Kingyumu/baobao/src/state.rs

//! 应用状态机 — 传感器读数、页面、闹钟、气压趋势等业务逻辑。
//!
//! 与 UI（display/render）和网络（network）解耦：主循环读硬件后更新 [`SystemState`]，
//! 渲染层只读 state，不直接访问 I2C/WiFi。
//!
//! ## Rust 要点
//! - `enum`：用类型表达有限状态（页面、气压趋势），比魔法字符串安全
//! - `impl Enum { fn next(self) -> Self }`：`self` 按值传递，状态转换返回新枚举
//! - 环形缓冲区：`(idx + 1) % N` 实现固定长度历史，无 Vec 分配
//! - `Option<(u8,u8)>`：记录「某天是否已响铃」，避免同一天重复触发

use crate::config;
use crate::sensors::DateTime;

/// 根据最近 10 次气压采样比较前/后半段均值。
#[derive(Debug, Clone, Copy, PartialEq)]
pub enum PressureTrend {
    Rising,
    Stable,
    Falling,
}

/// 触摸屏短按在本地页与对方城市页之间切换。
#[derive(Debug, Clone, Copy, PartialEq)]
pub enum DisplayPage {
    Local,
    Partner,
}

impl DisplayPage {
    pub fn next(self) -> Self {
        match self {
            Self::Local => Self::Partner,
            Self::Partner => Self::Local,
        }
    }

    pub fn label(self) -> &'static str {
        match self {
            Self::Local => "本地",
            Self::Partner => "对方",
        }
    }
}

/// 从中国天气网 HTTP 接口解析出的室外数据。
#[derive(Debug, Clone)]
pub struct NetworkWeather {
    pub temp: f32,
    pub humidity: f32,
    pub text: heapless::String<32>,
    pub weather_code: heapless::String<8>,
}

/// 全局运行时状态（单线程主循环独占 `&mut`，无需 Arc/Mutex）。
pub struct SystemState {
    pub temperature: f32,
    pub humidity: f32,
    pub pressure: f32,
    pressure_history: [f32; 10],
    pressure_idx: usize,
    pub pressure_filled: bool,
    pub pressure_trend: PressureTrend,
    pub current_time: Option<DateTime>,
    pub weather_code: heapless::String<8>,
    pub wifi_connected: bool,
    pub network_weather: Option<NetworkWeather>,
    pub partner_weather: Option<NetworkWeather>,
    pub together_days: u32,
    pub animation_counter: u32,
    pub special_event: Option<&'static str>,
    special_event_handled: Option<(u8, u8)>, // (month, day) 已处理标记
    pub last_weather_update: u64,
    pub last_ntp_sync: u64,
    pub display_page: DisplayPage,
    temp_chart: [f32; config::TEMP_CHART_LEN],
    chart_idx: usize,
    chart_filled: bool,
    pub chart_tick: u32,
    last_chart_sample: u64,
    pub weather_alert_active: bool,
    weather_alert_until: u64,
    last_weather_alert: u64,
    last_hourly_chime: Option<(u8, u8, u8)>,
    alarm_handled: Option<(u8, u8)>,
}

impl SystemState {
    pub fn new() -> Self {
        let mut wc = heapless::String::new();
        wc.push_str("d01").unwrap();
        Self {
            temperature: 0.0,
            humidity: 0.0,
            pressure: 1013.0,
            pressure_history: [1013.0; 10],
            pressure_idx: 0,
            pressure_filled: false,
            pressure_trend: PressureTrend::Stable,
            current_time: None,
            weather_code: wc,
            wifi_connected: false,
            network_weather: None,
            partner_weather: None,
            together_days: 1,
            animation_counter: 0,
            special_event: None,
            special_event_handled: None,
            last_weather_update: 0,
            last_ntp_sync: 0,
            display_page: DisplayPage::Local,
            temp_chart: [20.0; config::TEMP_CHART_LEN],
            chart_idx: 0,
            chart_filled: false,
            chart_tick: 0,
            last_chart_sample: 0,
            weather_alert_active: false,
            weather_alert_until: 0,
            last_weather_alert: 0,
            last_hourly_chime: None,
            alarm_handled: None,
        }
    }

    /// 写入新气压并更新趋势（需凑满 10 点后才计算）。
    pub fn update_pressure(&mut self, p: f32) {
        self.pressure = p;
        self.pressure_history[self.pressure_idx] = p;
        self.pressure_idx = (self.pressure_idx + 1) % 10;
        if self.pressure_idx == 0 {
            self.pressure_filled = true;
        }
        if !self.pressure_filled {
            return;
        }
        // 前 5 点 vs 后 5 点均值差
        let (old, new) = self.pressure_history[..10].iter().enumerate().fold(
            (0.0f32, 0.0f32),
            |(o, n), (i, &v)| {
                if i < 5 {
                    (o + v, n)
                } else {
                    (o, n + v)
                }
            },
        );
        let diff = new / 5.0 - old / 5.0;
        self.pressure_trend = if diff > 0.5 {
            PressureTrend::Rising
        } else if diff < -0.5 {
            PressureTrend::Falling
        } else {
            PressureTrend::Stable
        };
    }

    pub fn trend_text(&self) -> &'static str {
        match self.pressure_trend {
            PressureTrend::Rising => "↑ 转晴",
            PressureTrend::Stable => "→ 平稳",
            PressureTrend::Falling => "↓ 转阴",
        }
    }

    pub fn update_time(&mut self, t: DateTime) {
        let today = (t.month, t.day);
        if self.special_event_handled.map(|d| d != today).unwrap_or(false) {
            self.special_event_handled = None;
        }
        self.check_special(&t);
        self.together_days = compute_together_days(&t);
        self.current_time = Some(t);
    }

    fn check_special(&mut self, t: &DateTime) {
        if t.month == config::BIRTHDAY_MONTH && t.day == config::BIRTHDAY_DAY {
            self.special_event = Some("生日快乐！");
            return;
        }
        for &(m, d, msg) in config::ANNIVERSARIES {
            if t.month == m && t.day == d {
                self.special_event = Some(msg);
                return;
            }
        }
        self.special_event = None;
    }

    pub fn should_handle_special_event(&self) -> bool {
        let Some(ev) = self.special_event else {
            return false;
        };
        let Some(t) = self.current_time else {
            return false;
        };
        let today = (t.month, t.day);
        self.special_event_handled != Some(today) && !ev.is_empty()
    }

    pub fn mark_special_event_handled(&mut self) {
        if let Some(t) = self.current_time {
            self.special_event_handled = Some((t.month, t.day));
        }
    }

    /// 主界面图标：气压趋势可覆盖网络天气码。
    pub fn display_code(&self) -> &str {
        match self.pressure_trend {
            PressureTrend::Falling if self.pressure < 1000.0 => "trend_rain",
            PressureTrend::Rising if self.pressure > 1013.0 => "trend_sun",
            _ => self.weather_code.as_str(),
        }
    }

    pub fn set_weather_code(&mut self, code: &str) {
        self.weather_code.clear();
        let _ = self.weather_code.push_str(code);
    }

    pub fn next_page(&mut self) {
        self.display_page = self.display_page.next();
    }

    /// 每分钟采样一次室温，写入环形缓冲（供本地页折线图）。
    pub fn sample_temp_chart(&mut self, now: u64) {
        if now.saturating_sub(self.last_chart_sample) < config::TEMP_CHART_INTERVAL {
            return;
        }
        self.last_chart_sample = now;
        self.temp_chart[self.chart_idx] = self.temperature;
        self.chart_idx = (self.chart_idx + 1) % config::TEMP_CHART_LEN;
        if self.chart_idx == 0 {
            self.chart_filled = true;
        }
        self.chart_tick = self.chart_tick.wrapping_add(1);
    }

    pub fn temp_chart_count(&self) -> usize {
        if self.chart_filled {
            config::TEMP_CHART_LEN
        } else {
            self.chart_idx
        }
    }

    pub fn temp_chart_value(&self, i: usize) -> f32 {
        let n = self.temp_chart_count();
        if n == 0 {
            return self.temperature;
        }
        let start = if self.chart_filled {
            self.chart_idx
        } else {
            0
        };
        self.temp_chart[(start + i) % config::TEMP_CHART_LEN]
    }

    /// 气压骤降且绝对值偏低时触发变天预警（带冷却时间）。
    pub fn check_weather_alert(&mut self, now: u64) -> bool {
        if self.weather_alert_active {
            return false;
        }
        if now.saturating_sub(self.last_weather_alert) < config::WEATHER_ALERT_COOLDOWN {
            return false;
        }
        if !self.pressure_filled || self.pressure_trend != PressureTrend::Falling {
            return false;
        }
        if self.pressure >= 1005.0 {
            return false;
        }
        self.last_weather_alert = now;
        true
    }

    pub fn activate_weather_alert(&mut self, now: u64) {
        self.weather_alert_active = true;
        self.weather_alert_until = now + config::WEATHER_ALERT_DURATION;
    }

    pub fn tick_weather_alert(&mut self, now: u64) {
        if self.weather_alert_active && now >= self.weather_alert_until {
            self.weather_alert_active = false;
        }
    }

    pub fn weather_alert_showing(&self) -> bool {
        self.weather_alert_active
    }

    /// 整点报时：仅在 `:00` 的前 2 秒内触发一次。
    pub fn check_hourly_chime(&mut self, t: &DateTime) -> bool {
        if !config::HOURLY_CHIME_ENABLED {
            return false;
        }
        if t.minute != 0 || t.second >= 2 {
            return false;
        }
        if t.hour < config::HOURLY_CHIME_START || t.hour > config::HOURLY_CHIME_END {
            return false;
        }
        let key = (t.hour, t.day, t.month);
        if self.last_hourly_chime == Some(key) {
            return false;
        }
        self.last_hourly_chime = Some(key);
        true
    }

    /// 软件闹钟：到点响一次，同一天不重复。
    pub fn check_alarm(&mut self, t: &DateTime) -> bool {
        if !config::ALARM_ENABLED {
            return false;
        }
        if t.hour != config::ALARM_HOUR
            || t.minute != config::ALARM_MINUTE
            || t.second >= 2
        {
            return false;
        }
        let today = (t.month, t.day);
        if self.alarm_handled == Some(today) {
            return false;
        }
        self.alarm_handled = Some(today);
        true
    }
}

/// 从恋爱起始日算到今天（含起始日当天为第 1 天）。
pub fn compute_together_days(today: &DateTime) -> u32 {
    let start = civil_to_days(
        config::LOVE_START_YEAR,
        config::LOVE_START_MONTH,
        config::LOVE_START_DAY,
    );
    let end = civil_to_days(today.year, today.month, today.day);
    if end >= start {
        end - start + 1
    } else {
        1
    }
}

fn civil_to_days(year: u16, month: u8, day: u8) -> u32 {
    let mut y = year as u32;
    let m = month as u32;
    let d = day as u32;
    y -= if m <= 2 { 1 } else { 0 };
    let era = y / 400;
    let yoe = y - era * 400;
    let doy = (153 * (if m > 2 { m - 3 } else { m + 9 }) + 2) / 5 + d - 1;
    let doe = yoe * 365 + yoe / 4 - yoe / 100 + doy;
    era * 146097 + doe - 719468
}
